smaldragon/KITTY/Code/aquarius_8x8.png

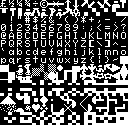
Code/aquarius_8x8.png
